distinctm1nd/krampus_minibadge_2023/schematic/krampus_cutout.kicad_sch

## KiCad design schematic/krampus_cutout.kicad_sch (2023-12-19)

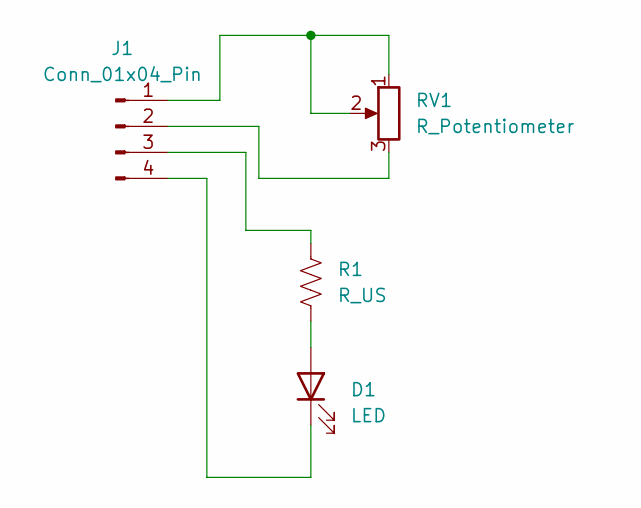
[picture p7: schematic krampus_cutout.kicad_sch]

Parts:
D1: LED; LED_0603_1608Metric_Pad1.05x0.95mm_HandSolder
J1: Conn_01x04_Pin; krampus_santa_connector
R1: R_US; R_0603_1608Metric_Pad0.98x0.95mm_HandSolder
RV1: R_Potentiometer; Potentiometer_Bourns_TC33X_Vertical

Connections:
unnamed: D1.1 (K), J1.4
unnamed: D1.2 (A), R1.2
unnamed: J1.1, RV1.1, RV1.2
unnamed: J1.2, RV1.3
unnamed: J1.3, R1.1
