distinctm1nd/krampus_minibadge_2023/schematic/krampus_with_potentiometer.kicad_sch

## KiCad design schematic/krampus_with_potentiometer.kicad_sch (2023-12-19)

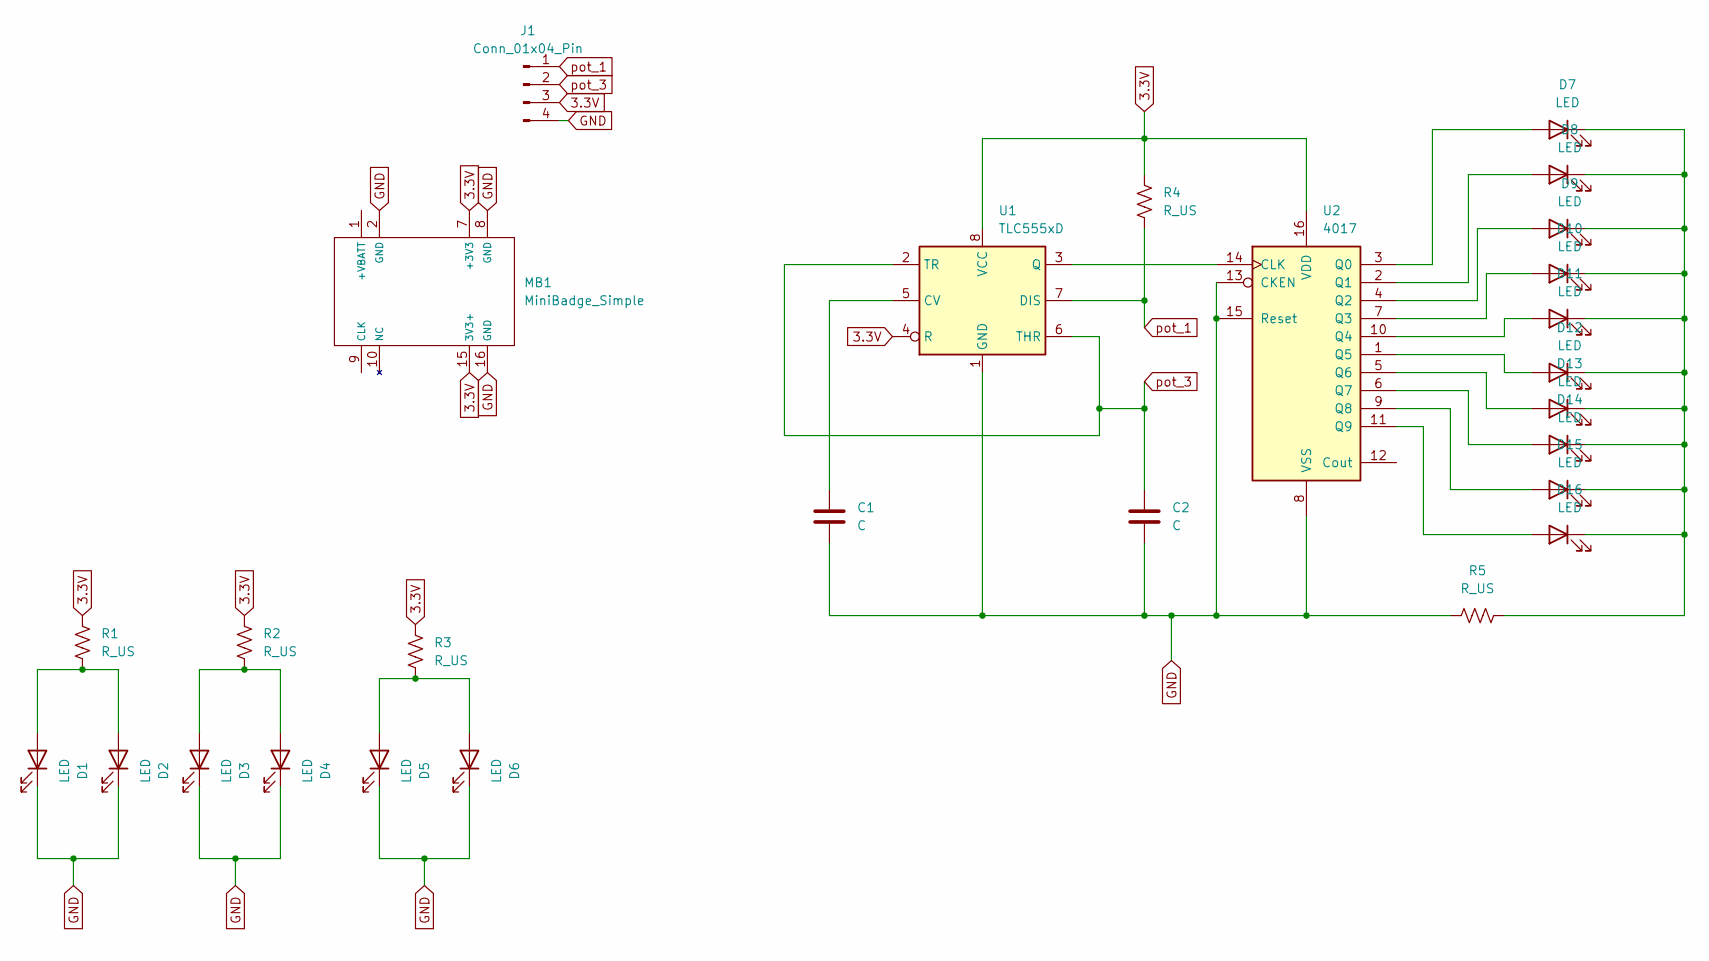
[picture p8: schematic krampus_with_potentiometer.kicad_sch]

Parts:
C1, C2: C; C_0603_1608Metric_Pad1.08x0.95mm_HandSolder
D1, D2, D3, D4, D5, D6: LED; LED_0603_1608Metric_Pad1.05x0.95mm_HandSolder
D7, D8, D9, D10, D11, D12, D13, D14, D15, D16: LED; LED_0402_1005Metric_Pad0.77x0.64mm_HandSolder
J1: Conn_01x04_Pin; krampus_santa_connector
MB1: MiniBadge_Simple
R1, R2, R3, R4, R5: R_US; R_0402_1005Metric_Pad0.72x0.64mm_HandSolder
U1: TLC555xD; SOIC-8_3.9x4.9mm_P1.27mm
U2: 4017; SOIC-16_4.55x10.3mm_P1.27mm

Connections:
3.3V: J1.3, MB1.7 (+3V3), MB1.15 (3V3+), R1.1, R2.1, R3.1, R4.1, U1.4 (R), U1.8 (VCC), U2.16 (VDD)
GND: C1.2, C2.2, D1.1 (K), D2.1 (K), D3.1 (K), D4.1 (K), D5.1 (K), D6.1 (K), J1.4, MB1.2 (GND), MB1.8 (GND), MB1.16 (GND), R5.1, U1.1 (GND), U2.8 (VSS), U2.13 (CKEN), U2.15 (Reset)
unnamed: C1.1, U1.5 (CV)
unnamed: D1.2 (A), D2.2 (A), R1.2
unnamed: D3.2 (A), D4.2 (A), R2.2
unnamed: D5.2 (A), D6.2 (A), R3.2
unnamed: D7.2 (A), U2.3 (Q0)
unnamed: D8.2 (A), U2.2 (Q1)
unnamed: D9.2 (A), U2.4 (Q2)
unnamed: D7.1 (K), D8.1 (K), D9.1 (K), D10.1 (K), D11.1 (K), D12.1 (K), D13.1 (K), D14.1 (K), D15.1 (K), D16.1 (K), R5.2
unnamed: D10.2 (A), U2.7 (Q3)
unnamed: D11.2 (A), U2.10 (Q4)
unnamed: D12.2 (A), U2.1 (Q5)
unnamed: D13.2 (A), U2.5 (Q6)
unnamed: D14.2 (A), U2.6 (Q7)
unnamed: D15.2 (A), U2.9 (Q8)
unnamed: D16.2 (A), U2.11 (Q9)
unnamed: U1.3 (Q), U2.14 (CLK)
pot_1: J1.1, R4.2, U1.7 (DIS)
pot_3: C2.1, J1.2, U1.2 (TR), U1.6 (THR)
